ieb/UltrasonicAntifouling/ltspice/nchannel-softstart.asc

C1: polcap; 10µ; V=106M008ATE055 Rser=55m Lser=0 mfg="   ---" pn="   ---" type="   ---"
C2: polcap; 6.8m; Rser=3m Lser=0 mfg="   ---" pn="   ---" type="   ---"
C3: cap; 10nF
C4: cap; 10nF
C5: polcap; 10µ; V=106M008ATE055 Rser=55m Lser=0 mfg="   ---" pn="   ---" type="   ---"
D1: schottky; BAT54
D2: schottky; BAT54
D3: schottky; BAT54
L1: ind; 0.01µ; Ipk=1.5 Rser=820m Rpar=1.171K Cpar=0 mfg="   ---" pn="   ---"
M1: nmos; IRF6607
R1: res; 10R
R2: res; 1R
R3: res; 100K
V1: voltage; 14; Rser=1
V2: voltage; PULSE(0 5 1 0 0 0.0005 0.001 2100)
V3: voltage; SINE(0 1 60000 3 0 0 60000)
Named nets: 0
.tran 10s startup
