ieb/UltrasonicAntifouling/ltspice/Draft1.asc

C1: polcap; 10µ; Rser=40m Lser=0 mfg="KEMET" pn="A700V106M12RATE040" type="Al electrolytic"
C2: polcap; 100µ; Rser=600m Lser=0 mfg="Nichicon" pn="UPG1E101MPH" type="Al electrolytic"
D1: schottky; 1N5819
D2: schottky; 1N5819
V1: voltage; PULSE(0 5 0 0 0 0.001 0.002 1000)
Named nets: 0
.tran 1s startup
