ieb/UltrasonicAntifouling/ltspice/filter.asc

C1: polcap; 6.8m; Rser=30m Lser=0 mfg="Nichicon" pn="UPR1E682MRH" type="Al electrolytic"
L1: ind; 220µ; Ipk=5.2 Rser=68.8m Rpar=25.434K Cpar=0 mfg="   ---" pn="   ---"
R1: res; 1
V1: voltage; SINE(14 1 10000); Rser=1 Cpar=1uF
V2: voltage; 14; Rser=0
Named nets: 0
.tran 1m
